antoniuflr/ProtoTone/Media/poza_fata.jpeg

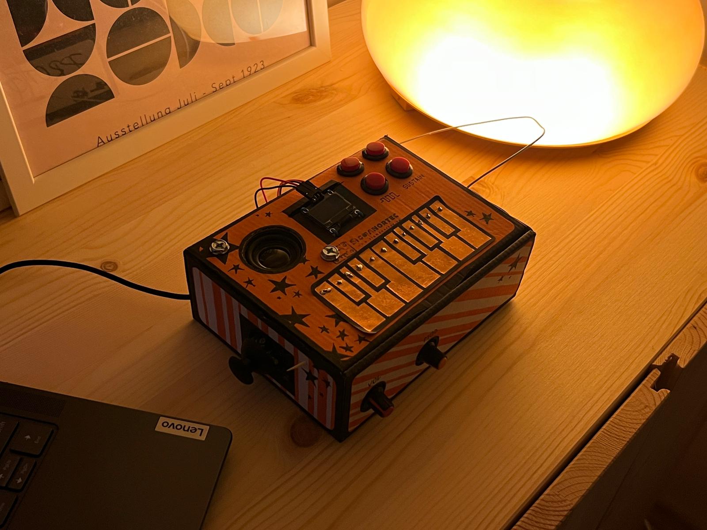
Media/poza_fata.jpeg
